JordanAceto/VCF_plug_in_boards/2164_SVF_plug_in_board/pics/pcb_rear.png

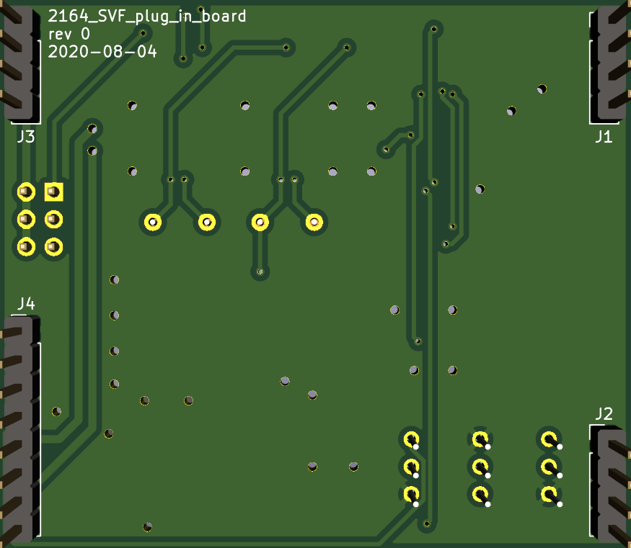
2164_SVF_plug_in_board/pics/pcb_rear.png
