JordanAceto/VCF_plug_in_boards/arp_4072_LPF_plug_in_board/pics/pcb_rear.png

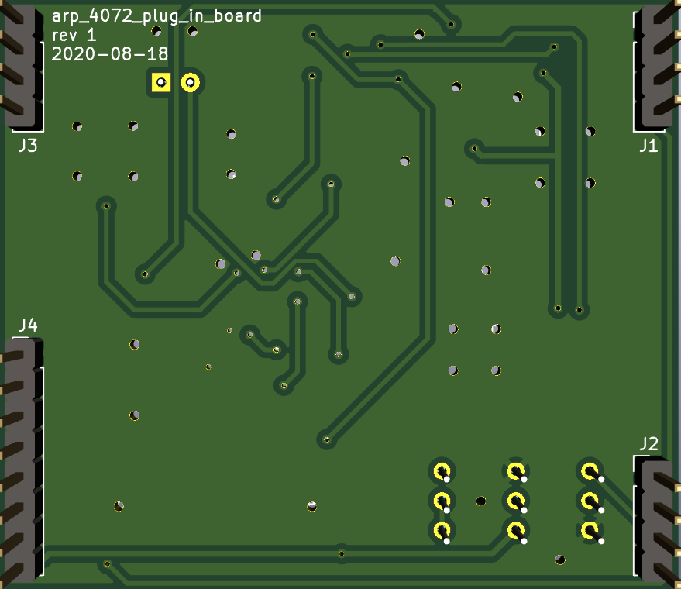
arp_4072_LPF_plug_in_board/pics/pcb_rear.png
