JordanAceto/VCF_plug_in_boards/assets/standard_dimensions.png

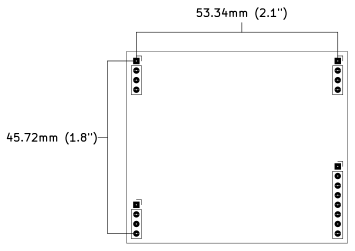
assets/standard_dimensions.png
