JordanAceto/VCF_plug_in_boards/CEM3320_LPF_plug_in_board/pics/pcb_rear.png

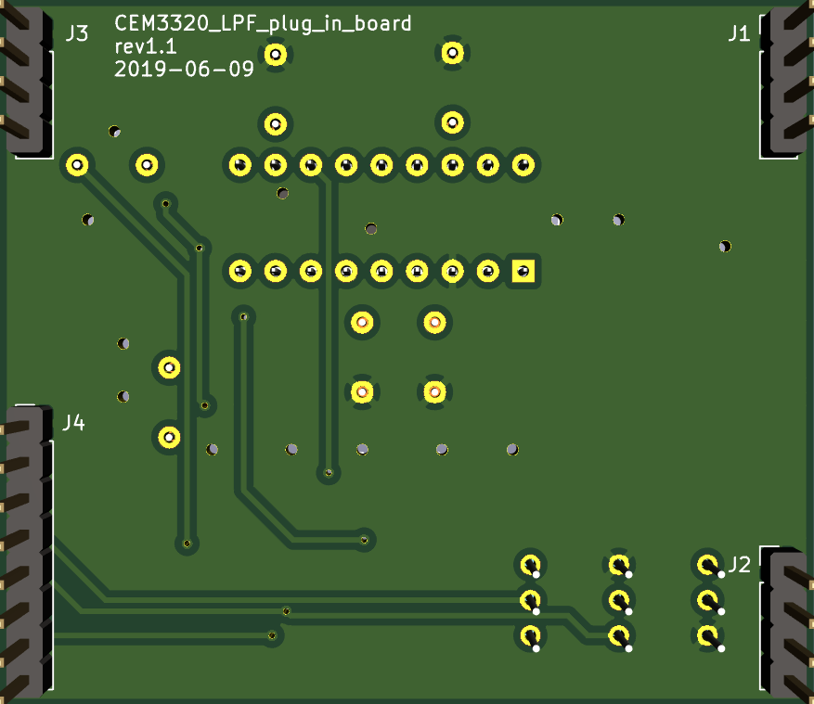
CEM3320_LPF_plug_in_board/pics/pcb_rear.png
