JordanAceto/VCF_plug_in_boards/late_MS20_VCF_plug_in_board/docs/html_nav/images/cat_pcb_bottom_jpg_late_MS20_VCF_plug_in_board-bottom.png

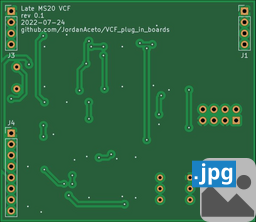
late_MS20_VCF_plug_in_board/docs/html_nav/images/cat_pcb_bottom_jpg_late_MS20_VCF_plug_in_board-bottom.png
