JordanAceto/VCF_plug_in_boards/late_MS20_VCF_plug_in_board/docs/html_nav/images/cat_pcb_top_jpg_late_MS20_VCF_plug_in_board-top.png

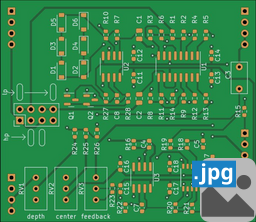
late_MS20_VCF_plug_in_board/docs/html_nav/images/cat_pcb_top_jpg_late_MS20_VCF_plug_in_board-top.png
