JordanAceto/VCF_plug_in_boards/late_MS20_VCF_plug_in_board/docs/html_nav/images/cat_pdf_layers_late_MS20_VCF_plug_in_board-B_Paste.png

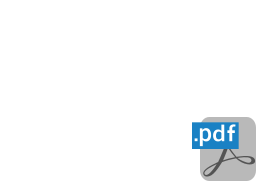
late_MS20_VCF_plug_in_board/docs/html_nav/images/cat_pdf_layers_late_MS20_VCF_plug_in_board-B_Paste.png
