JordanAceto/VCF_plug_in_boards/minimoog_LPF_plug_in_board/docs/html_nav/images/cat_pcb_top_jpg_minimoog_LPF-top.png

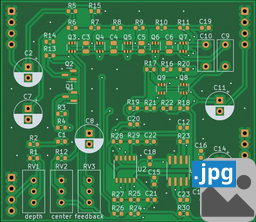
minimoog_LPF_plug_in_board/docs/html_nav/images/cat_pcb_top_jpg_minimoog_LPF-top.png
