JordanAceto/VCF_plug_in_boards/mutron_III_plug_in_board/pics/pcb_rear.png

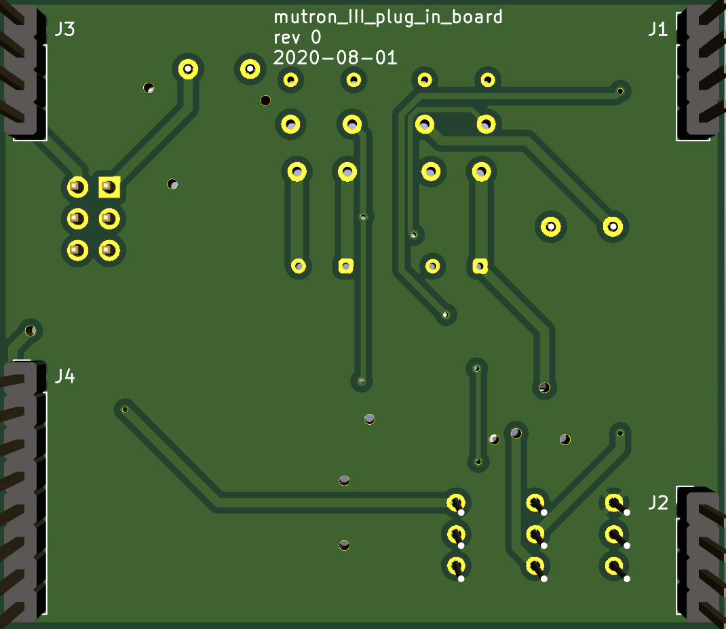
mutron_III_plug_in_board/pics/pcb_rear.png
