JordanAceto/VCF_plug_in_boards/SSI2140_LPF_plug_in_board/pics/pcb_rear.png

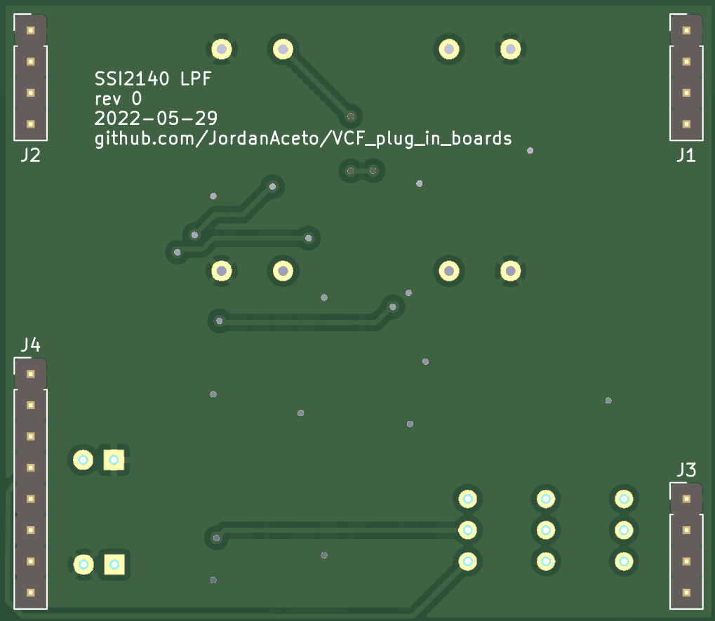
SSI2140_LPF_plug_in_board/pics/pcb_rear.png
