JordanAceto/VCF_plug_in_boards/late_MS20_VCF_plug_in_board/docs/html_nav/images/cat_pdf_sch_print_late_MS20_VCF_plug_in_board-schematic.png

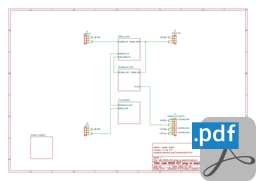
late_MS20_VCF_plug_in_board/docs/html_nav/images/cat_pdf_sch_print_late_MS20_VCF_plug_in_board-schematic.png
