JordanAceto/VCF_plug_in_boards/minimoog_LPF_plug_in_board/docs/html_nav/images/cat_pdf_sch_print_minimoog_LPF-schematic.png

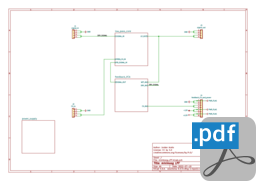
minimoog_LPF_plug_in_board/docs/html_nav/images/cat_pdf_sch_print_minimoog_LPF-schematic.png
