JordanAceto/VCF_plug_in_boards/late_MS20_VCF_plug_in_board/docs/2D/late_MS20_VCF_plug_in_board-F_Cu.pdf

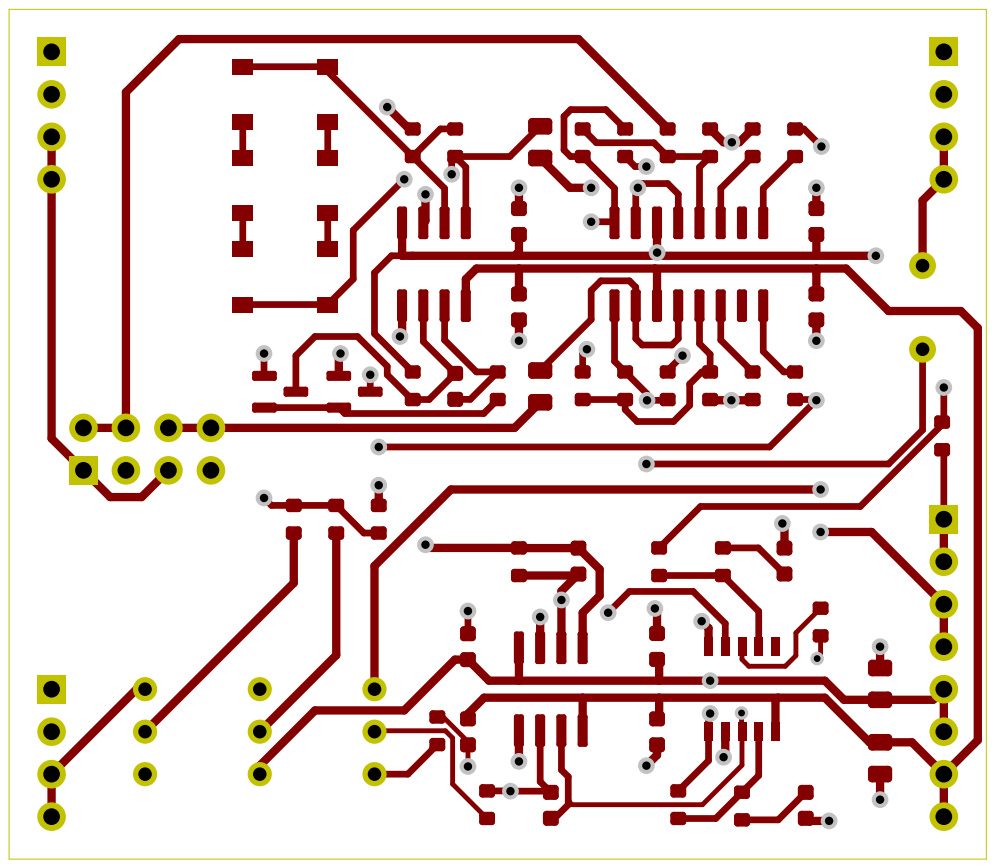
[picture p83: page 1]
