JordanAceto/VCF_plug_in_boards/minimoog_LPF_plug_in_board/docs/2D/minimoog_LPF-B_Cu.pdf

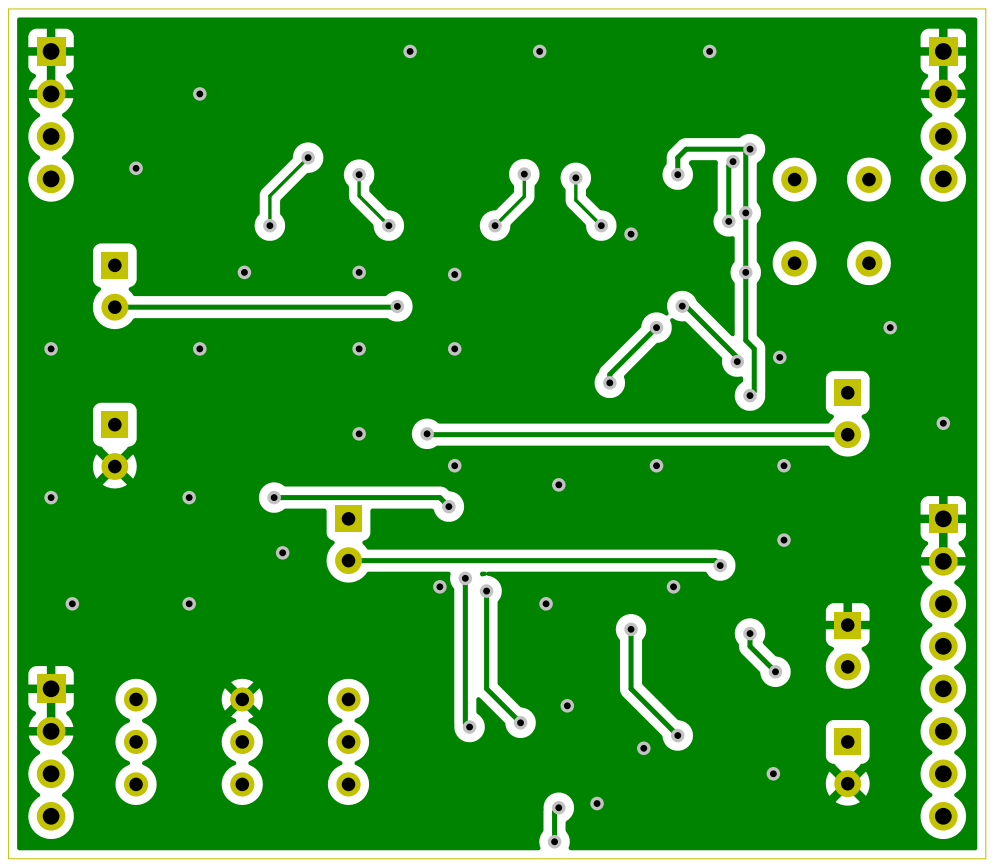
[picture p84: page 1]
