JordanAceto/VCF_plug_in_boards/minimoog_LPF_plug_in_board/docs/2D/minimoog_LPF-F_Cu.pdf

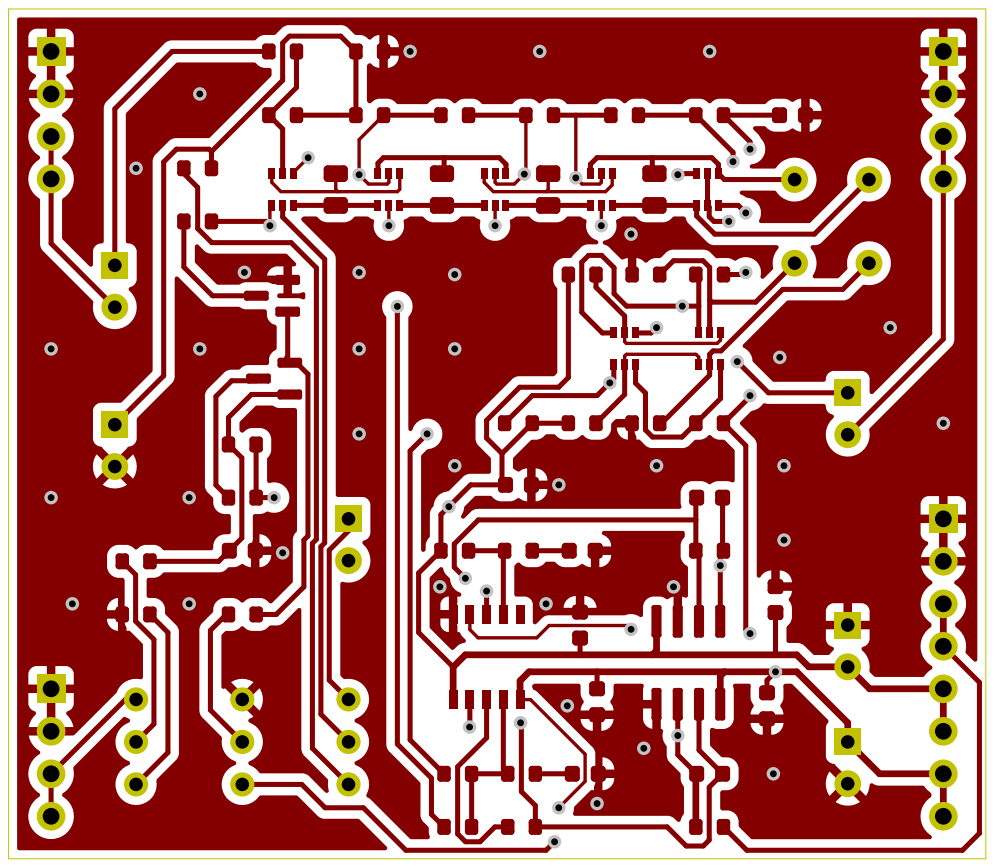
[picture p85: page 1]
