JordanAceto/VCF_plug_in_boards/late_MS20_VCF_plug_in_board/docs/2D/individual_layers/late_MS20_VCF_plug_in_board-B_Fab.pdf

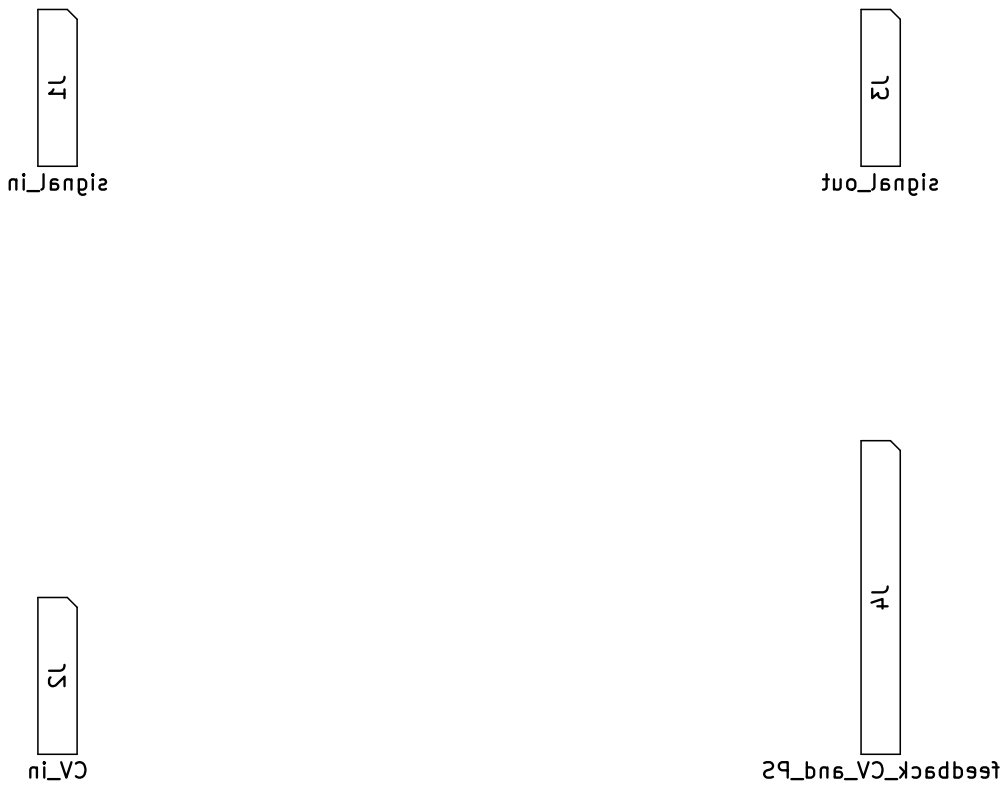
[picture p87: page 1]
