JordanAceto/VCF_plug_in_boards/late_MS20_VCF_plug_in_board/docs/2D/individual_layers/late_MS20_VCF_plug_in_board-B_Silkscreen.pdf

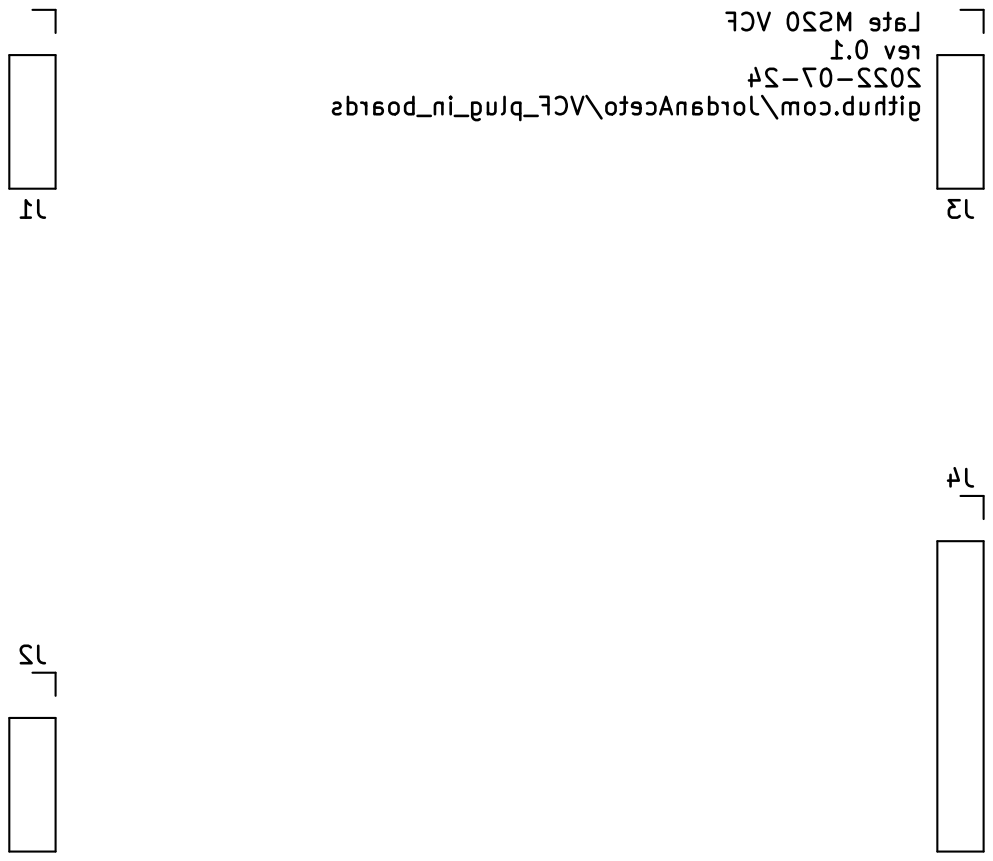
[picture p89: page 1]
