JordanAceto/VCF_plug_in_boards/late_MS20_VCF_plug_in_board/docs/2D/individual_layers/late_MS20_VCF_plug_in_board-F_Courtyard.pdf

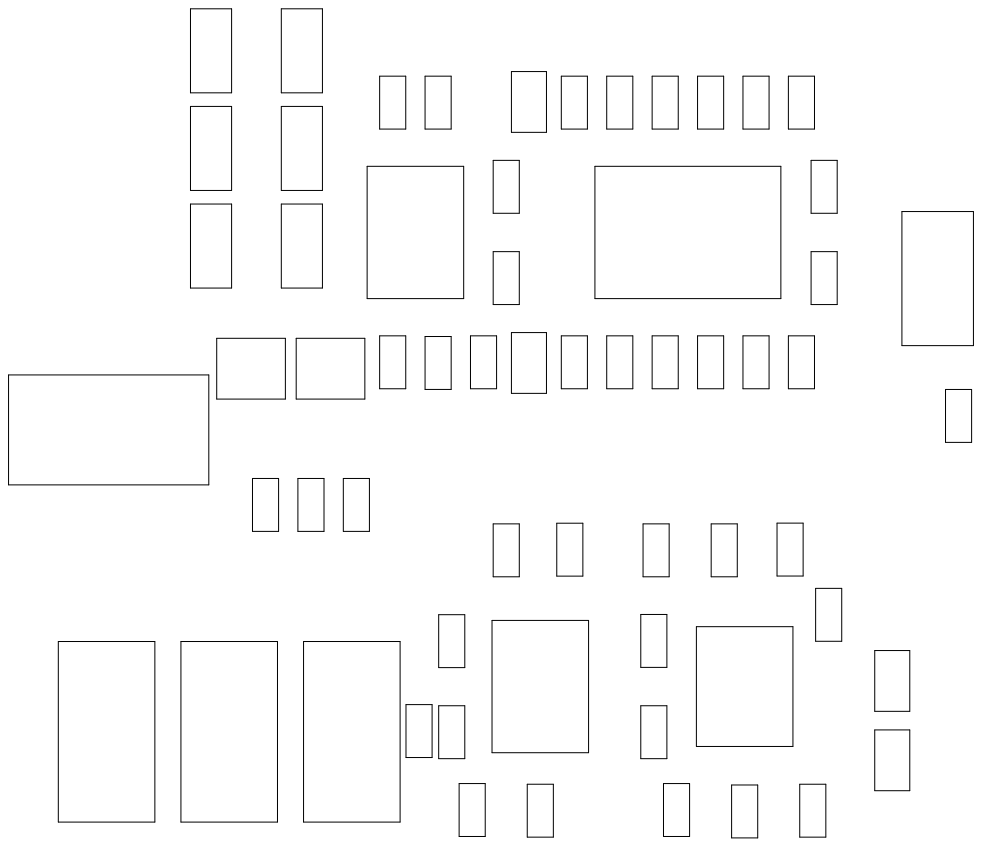
[picture p90: page 1]
