JordanAceto/VCF_plug_in_boards/minimoog_LPF_plug_in_board/docs/2D/individual_layers/minimoog_LPF-B_Mask.pdf

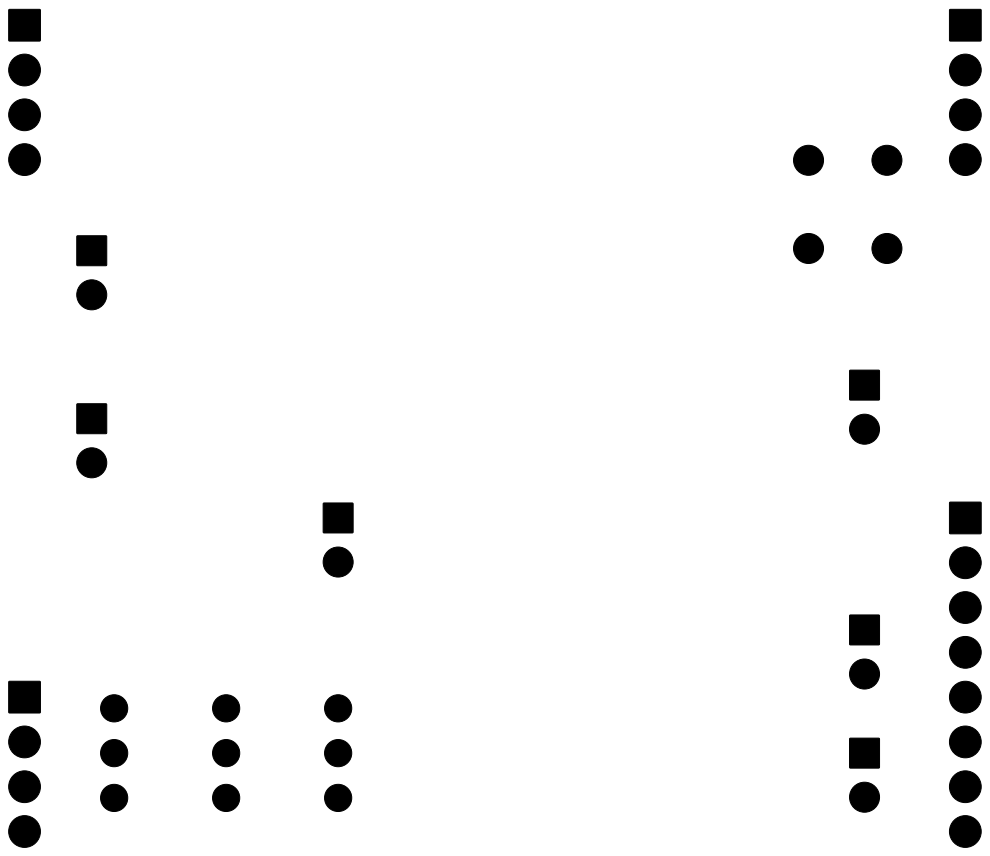
[picture p97: page 1]
