JordanAceto/VCF_plug_in_boards/minimoog_LPF_plug_in_board/docs/2D/individual_layers/minimoog_LPF-F_Courtyard.pdf

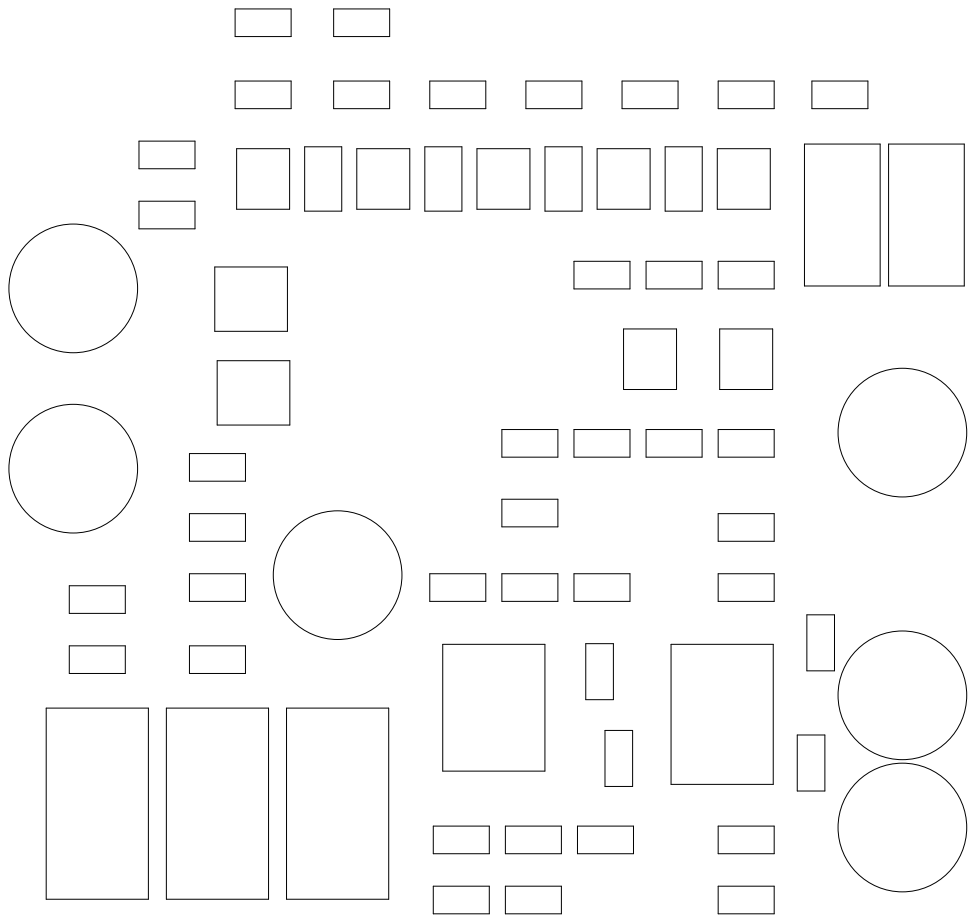
[picture p99: page 1]
