JordanAceto/VCF_plug_in_boards/haible_2040_LPF_plug_in_board/kicad_docs/haible_2040_LPF_plug_in_board.kicad_pcb

## KiCad design haible_2040_LPF_plug_in_board/kicad_docs/haible_2040_LPF_plug_in_board.kicad_pcb (2020-08-01)

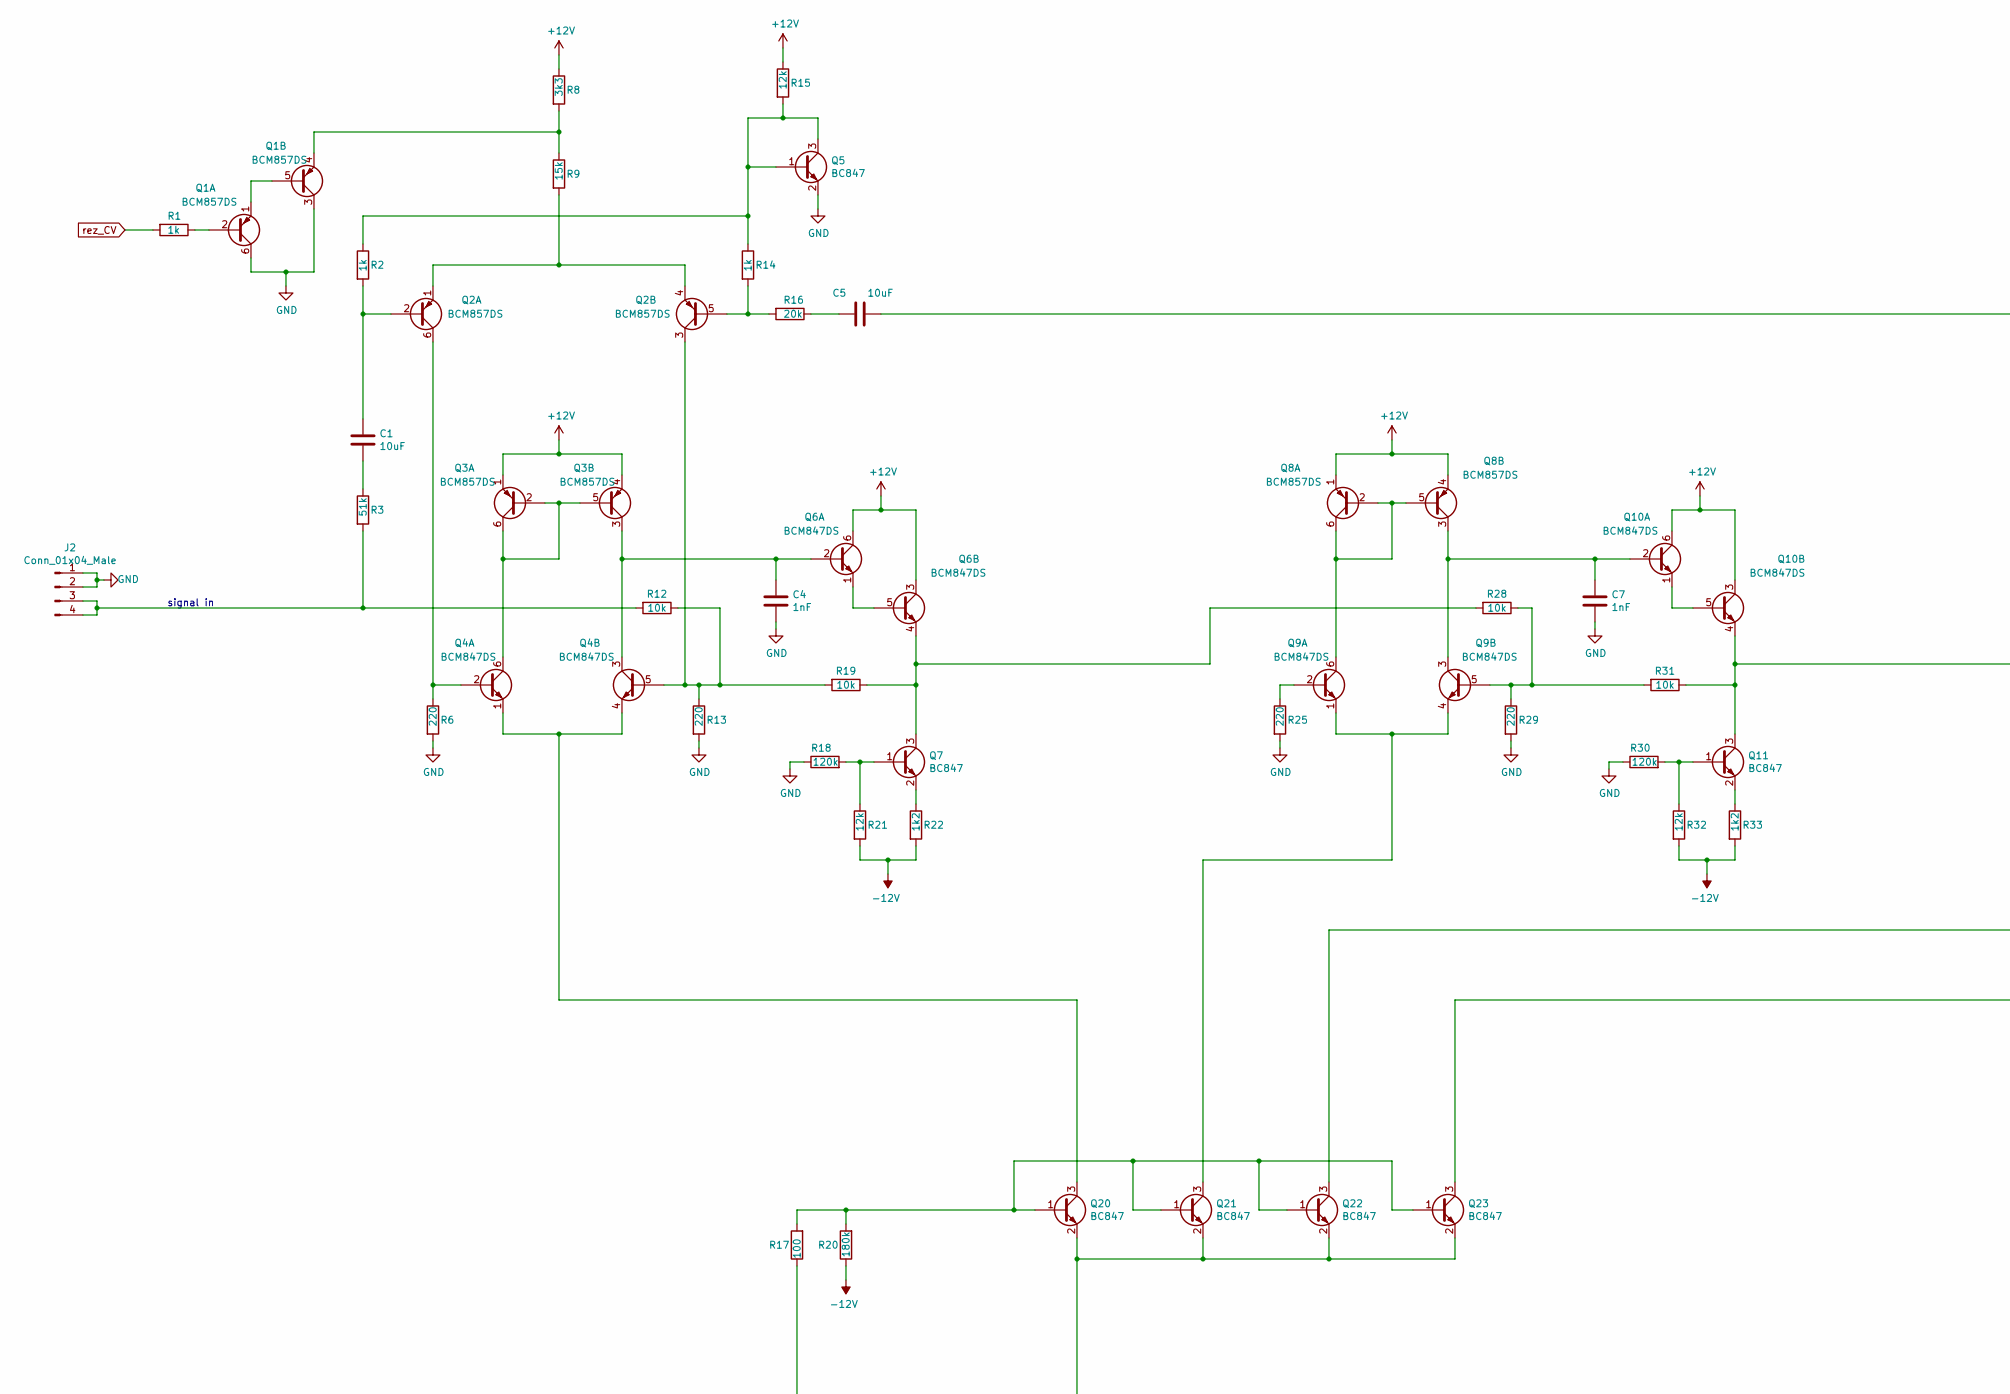
[picture p173: schematic haible_2040_LPF_plug_in_board.sch, Haible 2040 LPF plug-in board, part in row 1, column 1]

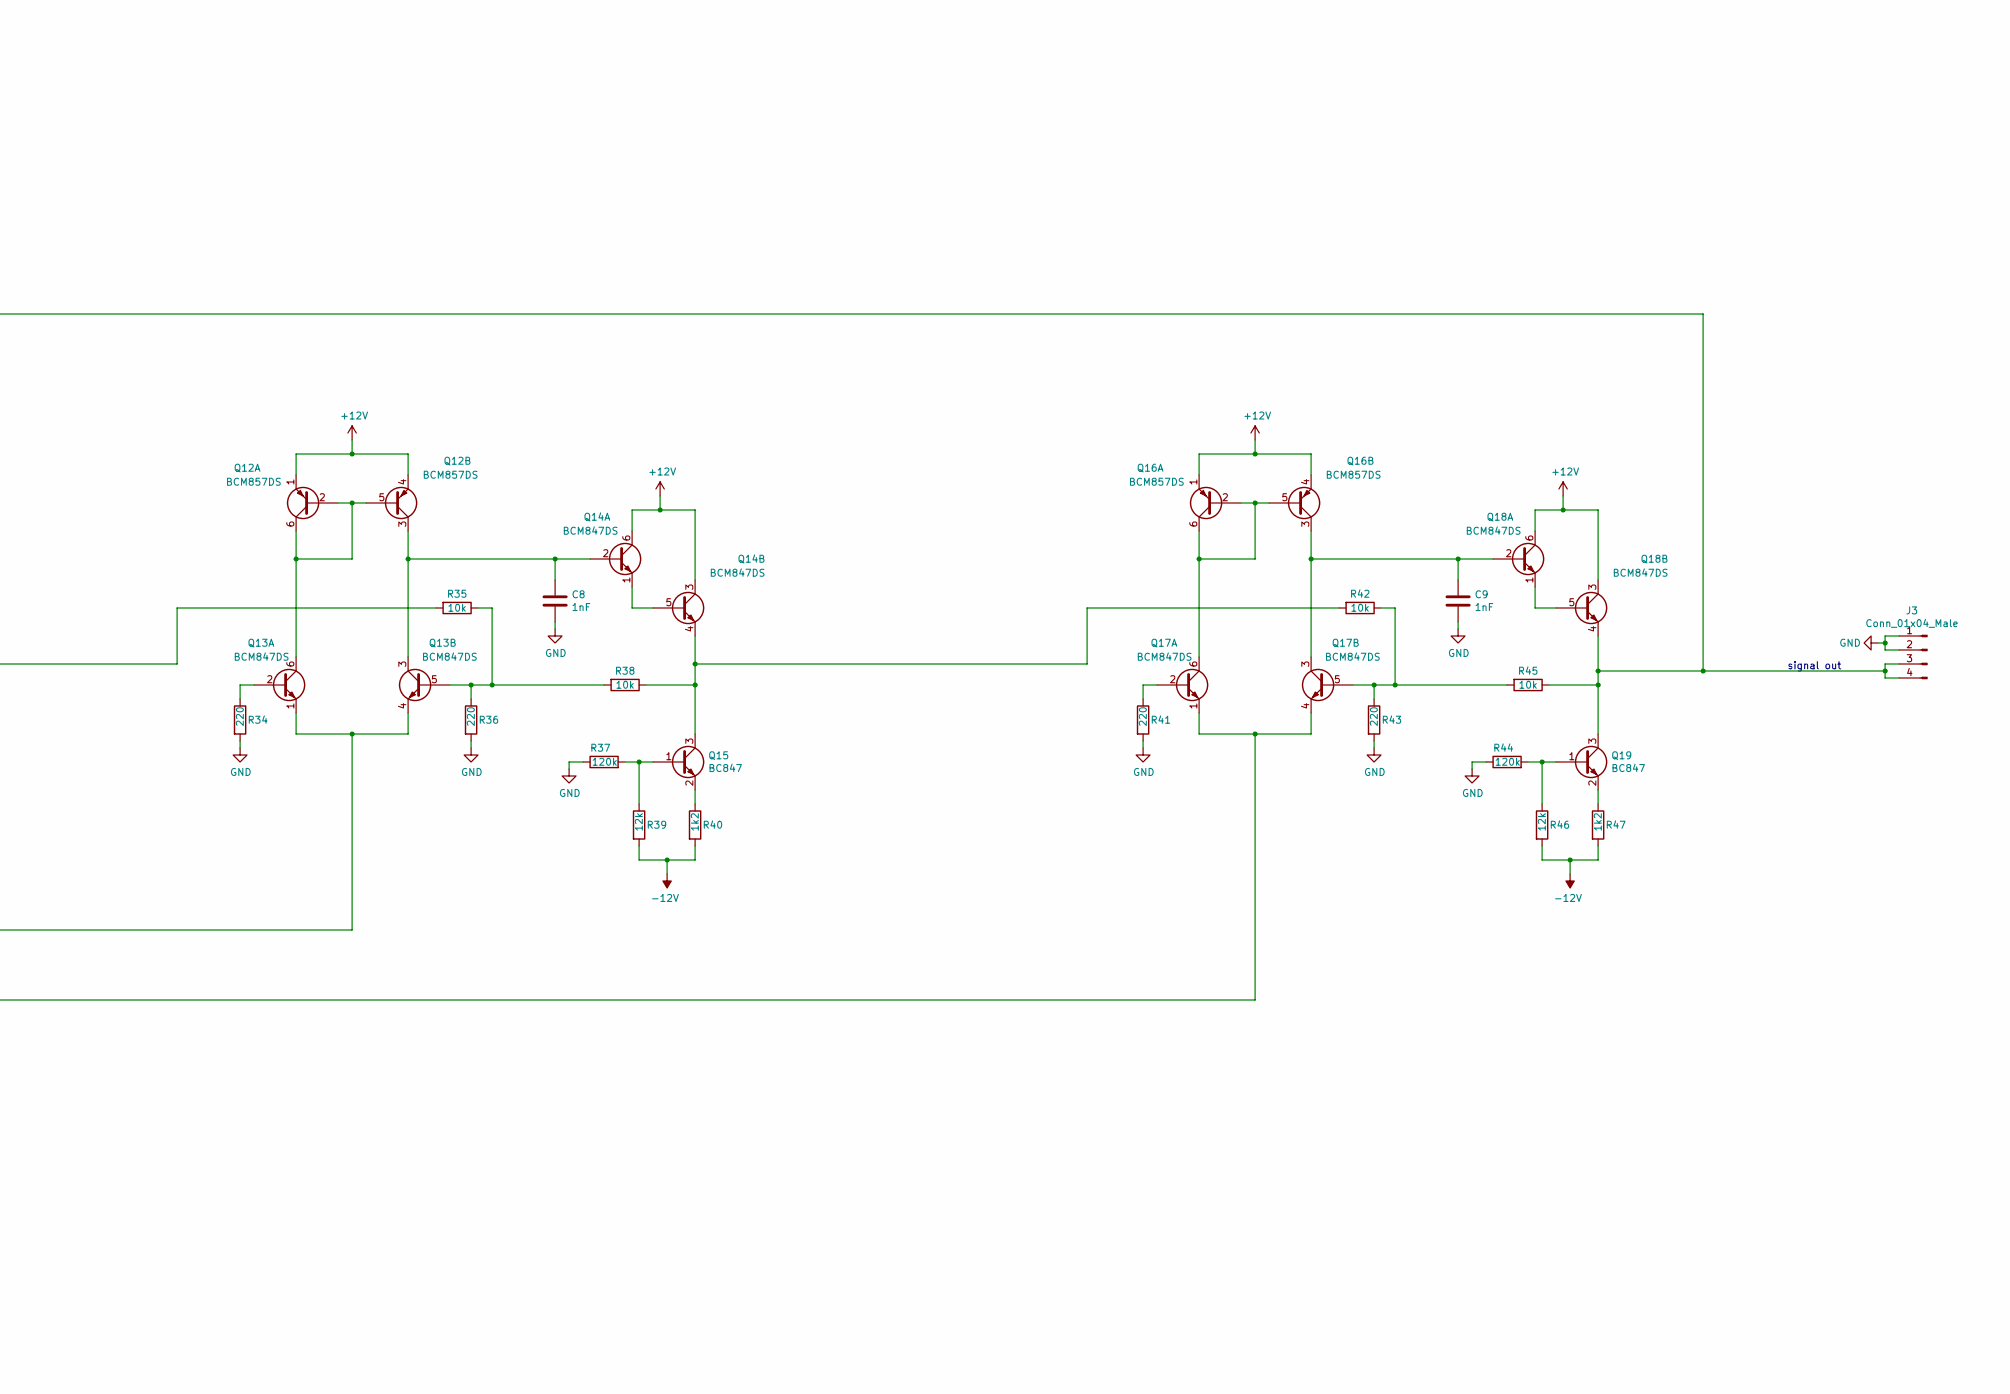
[picture p174: schematic haible_2040_LPF_plug_in_board.sch, Haible 2040 LPF plug-in board, part in row 1, column 2]

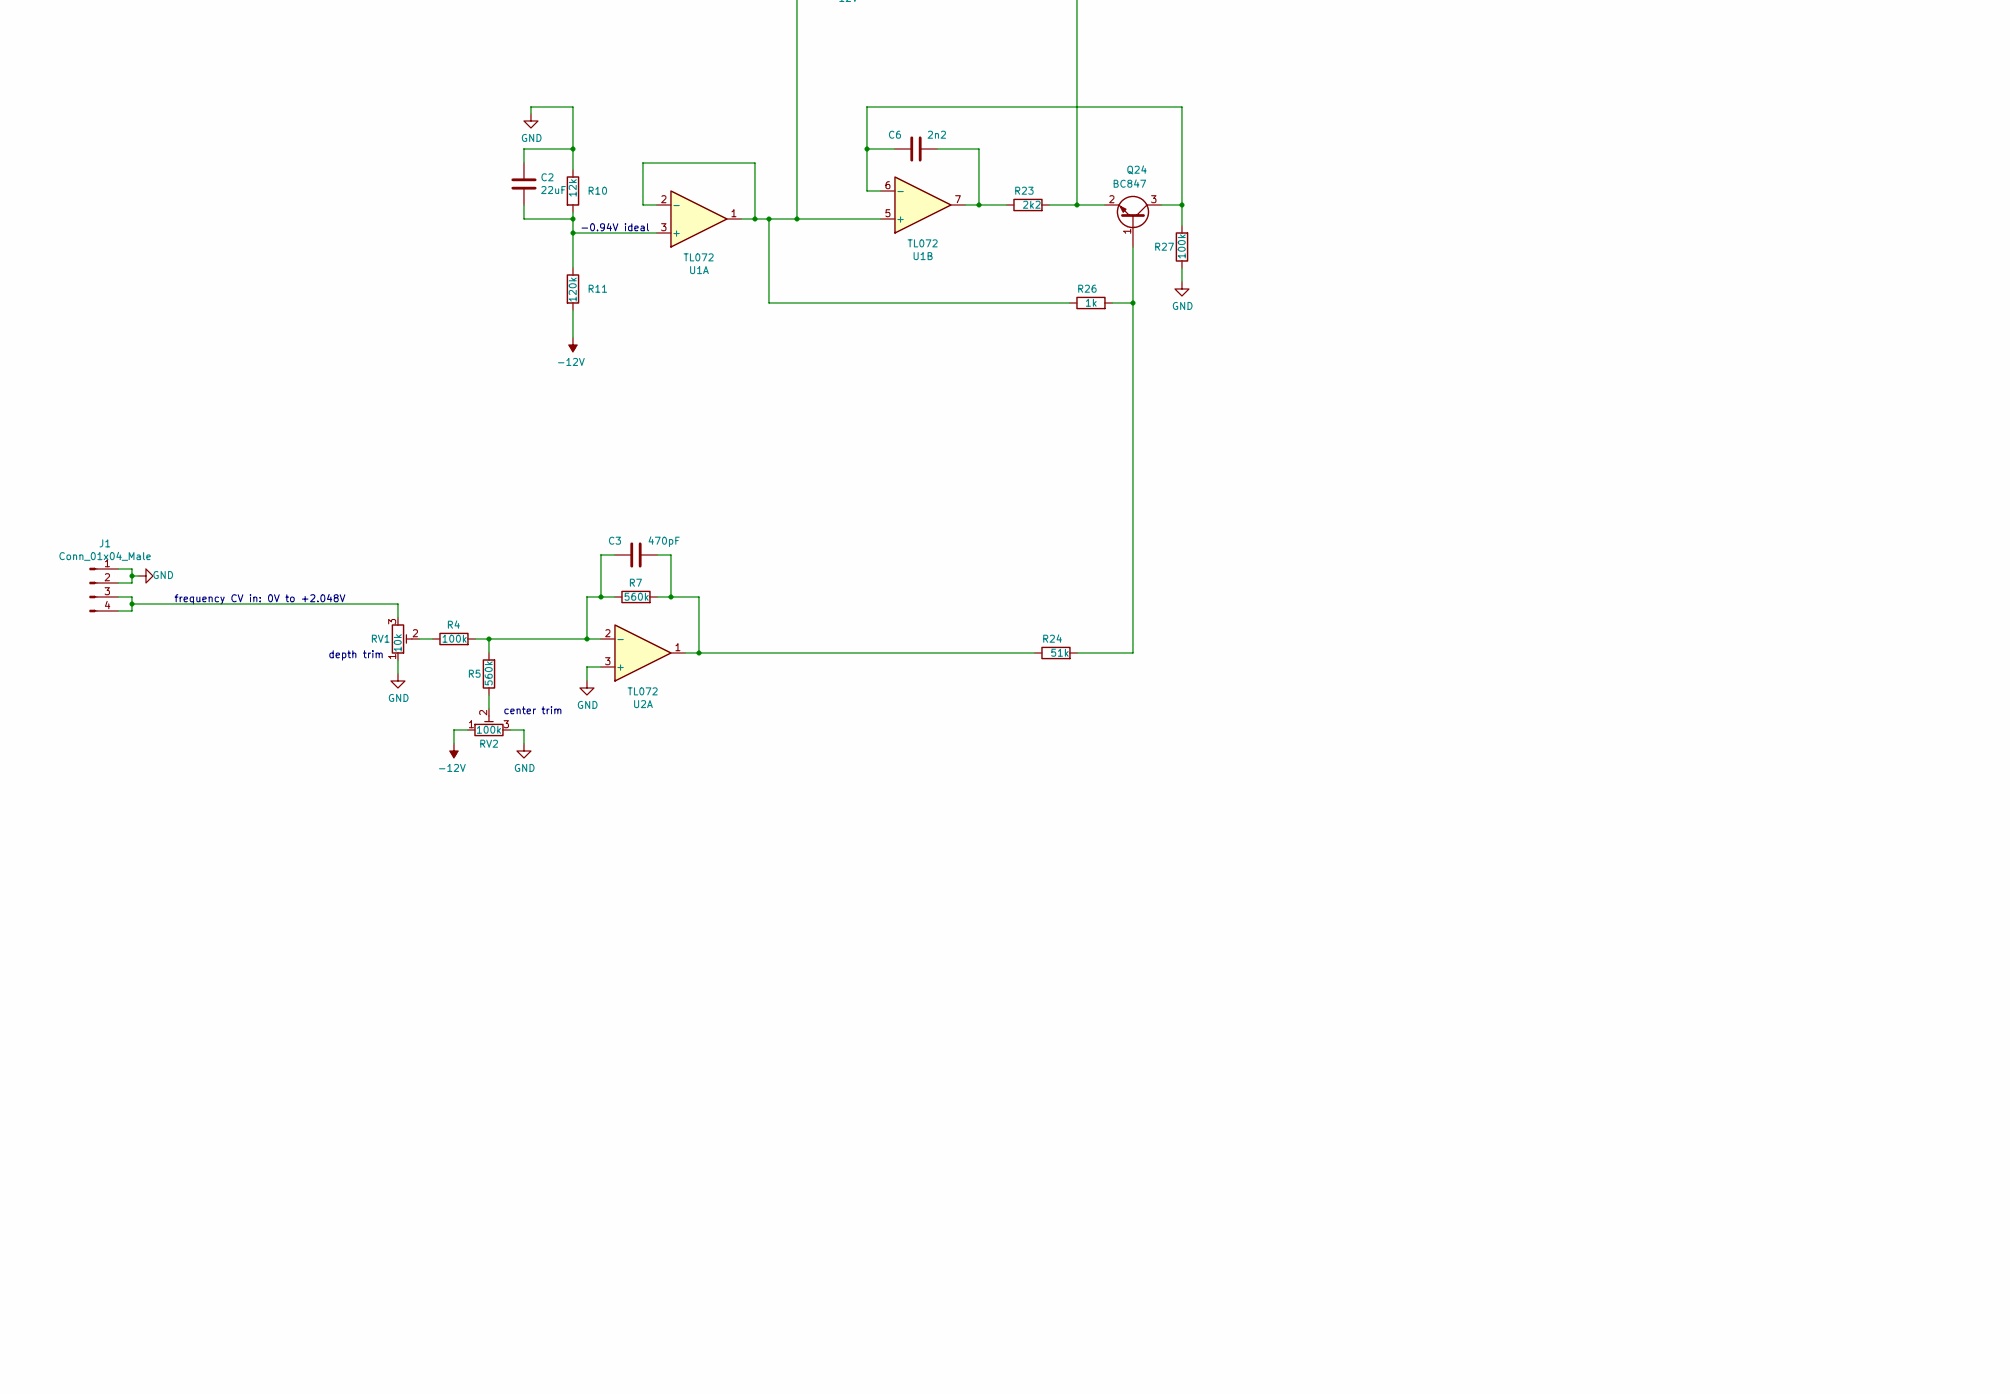
[picture p175: schematic haible_2040_LPF_plug_in_board.sch, Haible 2040 LPF plug-in board, part in row 2, column 1]

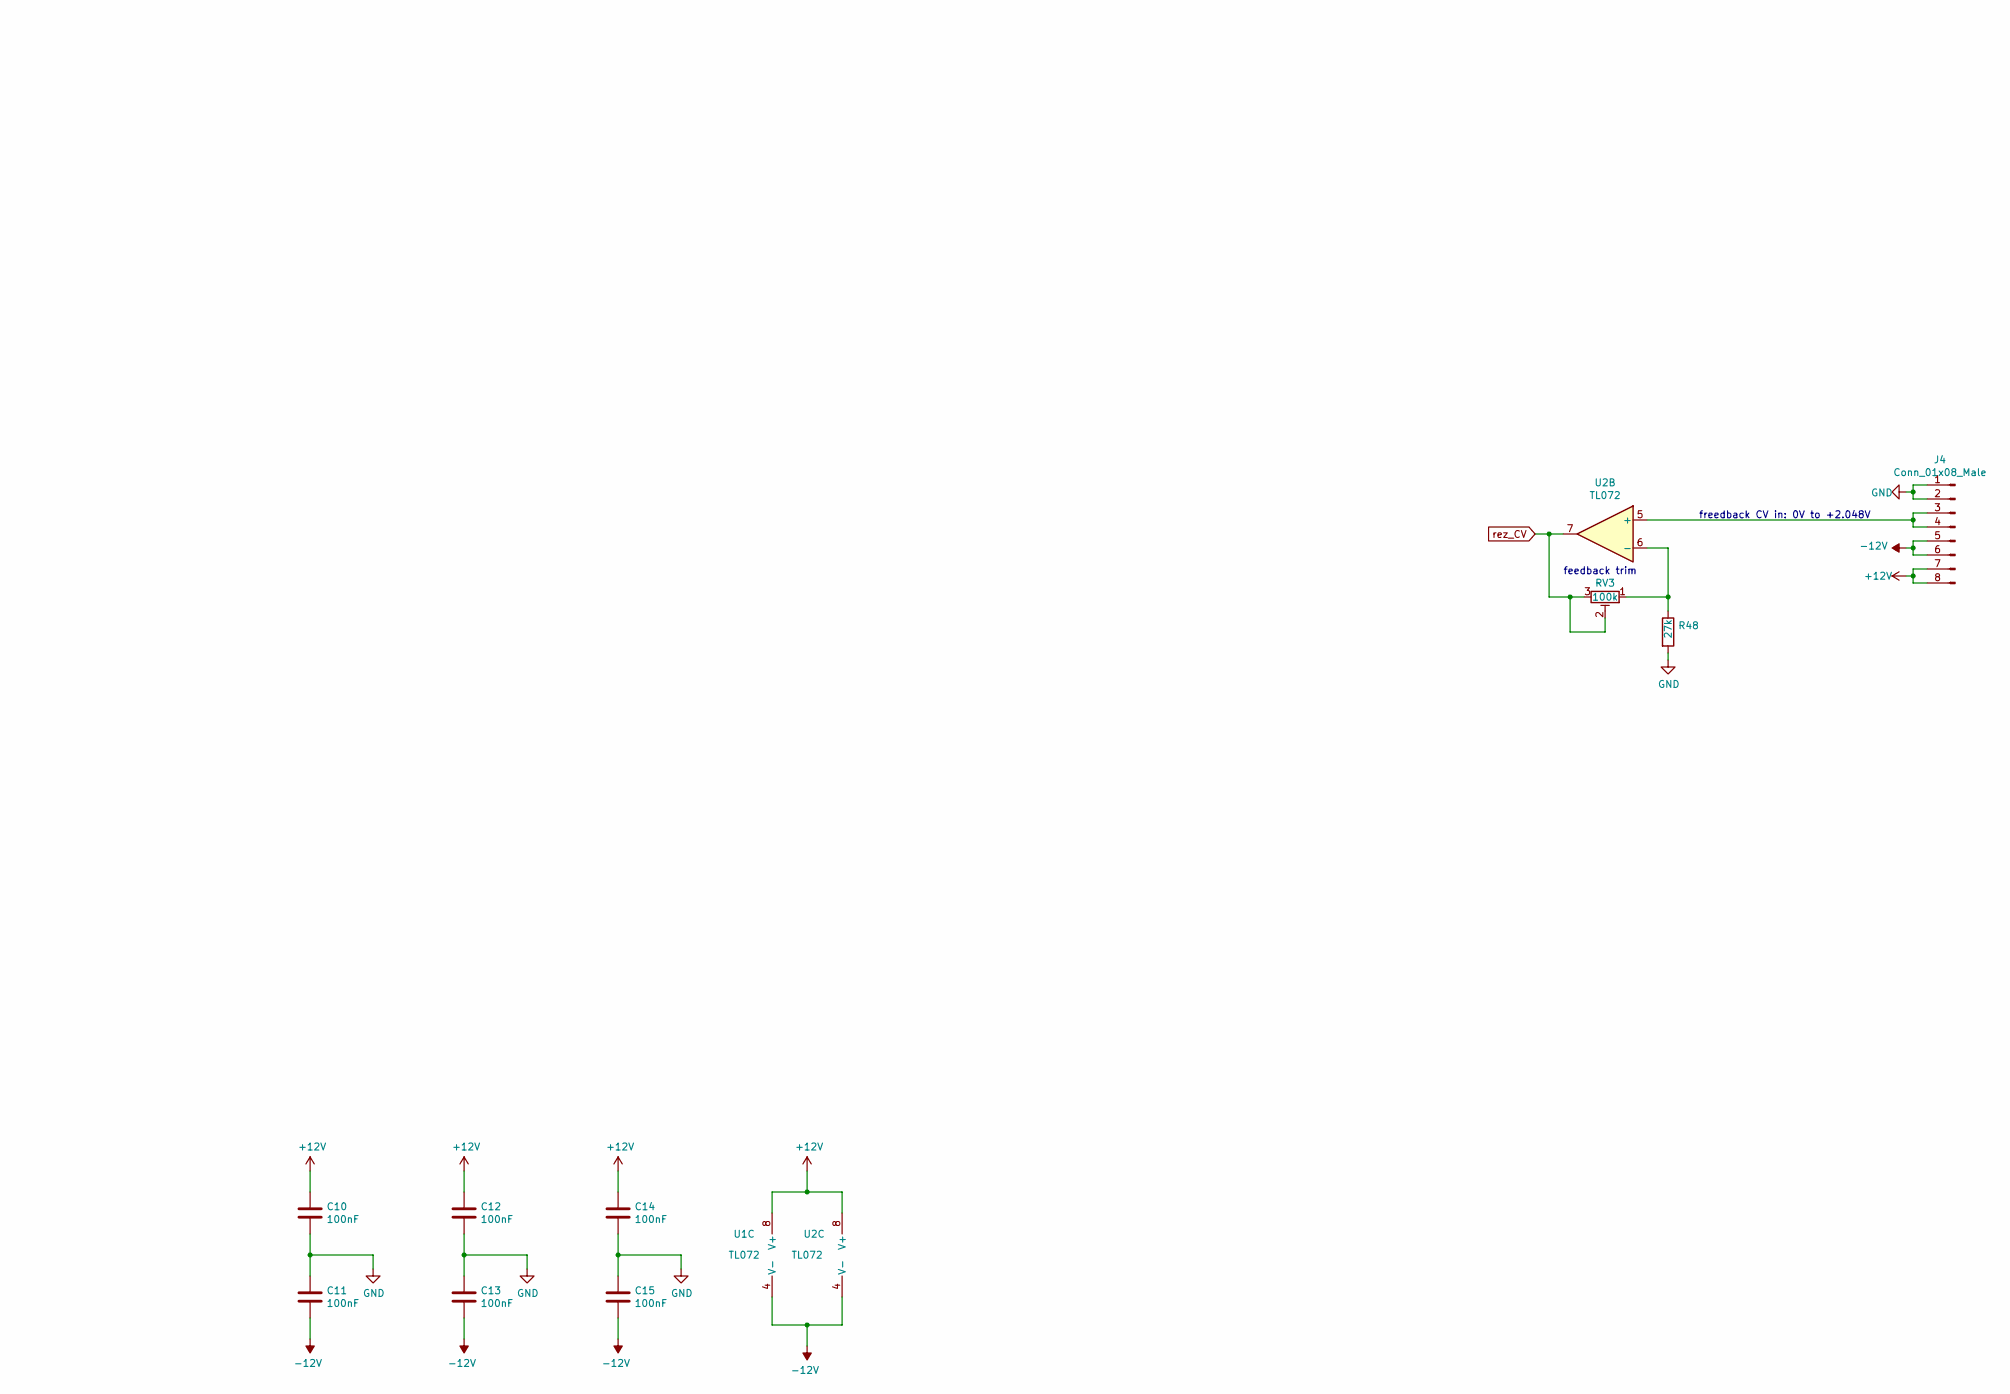
[picture p176: schematic haible_2040_LPF_plug_in_board.sch, Haible 2040 LPF plug-in board, part in row 2, column 2]

Parts:
C1, C5: 10uF; C_Radial_D6.3mm_H11.0mm_P2.50mm
C2: 22uF; C_0805_2012Metric_Pad1.15x1.40mm_HandSolder
C3: 470pF; C_0805_2012Metric_Pad1.15x1.40mm_HandSolder
C4, C7, C8, C9: 1nF; C_0805_2012Metric_Pad1.15x1.40mm_HandSolder
C6: 2n2; C_0805_2012Metric_Pad1.15x1.40mm_HandSolder
C10, C11, C12, C13, C14, C15: 100nF; C_0805_2012Metric_Pad1.15x1.40mm_HandSolder
J1, J2, J3: Conn_01x04_Male; PinHeader_1x04_P2.54mm_Vertical
J4: Conn_01x08_Male; PinHeader_1x08_P2.54mm_Vertical
Q1, Q2, Q3, Q8, Q12, Q16: BCM857DS; SOT457
Q4, Q6, Q9, Q10, Q13, Q14, Q17, Q18: BCM847DS; SOT457
Q5, Q7, Q11, Q15, Q19, Q20, Q21, Q22, Q23, Q24: BC847; SOT-23_Handsoldering
R1, R2, R14, R26: 1k; R_0805_2012Metric_Pad1.15x1.40mm_HandSolder
R3, R24: 51k; R_0805_2012Metric_Pad1.15x1.40mm_HandSolder
R4, R27: 100k; R_0805_2012Metric_Pad1.15x1.40mm_HandSolder
R5, R7: 560k; R_0805_2012Metric_Pad1.15x1.40mm_HandSolder
R6, R13, R25, R29, R34, R36, R41, R43: 220; R_0805_2012Metric_Pad1.15x1.40mm_HandSolder
R8: 3k3; R_0805_2012Metric_Pad1.15x1.40mm_HandSolder
R9: 15k; R_0805_2012Metric_Pad1.15x1.40mm_HandSolder
R10, R15, R21, R32, R39, R46: 12k; R_0805_2012Metric_Pad1.15x1.40mm_HandSolder
R11, R18, R30, R37, R44: 120k; R_0805_2012Metric_Pad1.15x1.40mm_HandSolder
R12, R19, R28, R31, R35, R38, R42, R45: 10k; R_0805_2012Metric_Pad1.15x1.40mm_HandSolder
R16: 20k; R_0805_2012Metric_Pad1.15x1.40mm_HandSolder
R17: 100; R_0805_2012Metric_Pad1.15x1.40mm_HandSolder
R20: 180k; R_0805_2012Metric_Pad1.15x1.40mm_HandSolder
R22, R33, R40, R47: 1k2; R_0805_2012Metric_Pad1.15x1.40mm_HandSolder
R23: 2k2; R_0805_2012Metric_Pad1.15x1.40mm_HandSolder
R48: 27k; R_0805_2012Metric_Pad1.15x1.40mm_HandSolder
RV1: 10k; Potentiometer_Bourns_3269W_Vertical
RV2, RV3: 100k; Potentiometer_Bourns_3269W_Vertical
U1, U2: TL072; SOIC-8_3.9x4.9mm_P1.27mm

Connections:
+12V: C10.1, C12.1, C14.1, J4.7, J4.8, Q3.1 (E), Q3.4 (E), Q6.3 (C), Q6.6 (C), Q8.1 (E), Q8.4 (E), Q10.3 (C), Q10.6 (C), Q12.1 (E), Q12.4 (E), Q14.3 (C), Q14.6 (C), Q16.1 (E), Q16.4 (E), Q18.3 (C), Q18.6 (C), R8.1, R15.1, U1.8 (V+), U2.8 (V+)
-12V: C11.2, C13.2, C15.2, J4.5, J4.6, R11.2, R20.1, R21.2, R22.2, R32.2, R33.2, R39.2, R40.2, R46.2, R47.2, RV2.1, U1.4 (V-), U2.4 (V-)
GND: C2.1, C4.2, C7.2, C8.2, C9.2, C10.2, C11.1, C12.2, C13.1, C14.2, C15.1, J1.1, J1.2, J2.1, J2.2, J3.1, J3.2, J4.1, J4.2, Q1.3 (C), Q1.6 (C), Q5.2 (E), R6.2, R10.1, R13.2, R18.1, R25.2, R27.1, R29.2, R30.1, R34.2, R36.2, R37.1, R41.2, R43.2, R44.1, R48.2, RV1.1, RV2.3, U2.3 (+)
unnamed: C1.1, Q2.2 (B), R2.2
unnamed: C1.2, R3.1
unnamed: C2.2, R10.2, R11.1, U1.3 (+)
unnamed: C3.1, R4.2, R5.2, R7.1, U2.2 (-)
unnamed: C3.2, R7.2, R24.1, U2.1
unnamed: C4.1, Q3.3 (C), Q4.3 (C), Q6.2 (B)
unnamed: C5.1, J3.3, J3.4, Q18.4 (E), Q19.3 (C), R45.1
unnamed: C5.2, R16.1
unnamed: C6.1, Q24.3 (C), R27.2, U1.6 (-)
unnamed: C6.2, R23.1, U1.7
unnamed: C7.1, Q8.3 (C), Q9.3 (C), Q10.2 (B)
unnamed: C8.1, Q12.3 (C), Q13.3 (C), Q14.2 (B)
unnamed: C9.1, Q16.3 (C), Q17.3 (C), Q18.2 (B)
unnamed: J1.3, J1.4, RV1.3
unnamed: J2.3, J2.4, R3.2, R12.2
unnamed: J4.3, J4.4, U2.5 (+)
unnamed: Q1.1 (E), Q1.5 (B)
unnamed: Q1.2 (B), R1.1
unnamed: Q1.4 (E), R8.2, R9.1
unnamed: Q2.1 (E), Q2.4 (E), R9.2
unnamed: Q2.3 (C), Q4.5 (B), R12.1, R13.1, R19.2
unnamed: Q2.5 (B), R14.2, R16.2
unnamed: Q2.6 (C), Q4.2 (B), R6.1
unnamed: Q3.2 (B), Q3.5 (B), Q3.6 (C), Q4.6 (C)
unnamed: Q5.1 (B), Q5.3 (C), R2.1, R14.1, R15.2
unnamed: Q6.1 (E), Q6.5 (B)
unnamed: Q6.4 (E), Q7.3 (C), R19.1, R28.2
unnamed: Q7.1 (B), R18.2, R21.1
unnamed: Q7.2 (E), R22.1
unnamed: Q8.2 (B), Q8.5 (B), Q8.6 (C), Q9.6 (C)
unnamed: Q9.2 (B), R25.1
unnamed: Q9.5 (B), R28.1, R29.1, R31.2
unnamed: Q10.1 (E), Q10.5 (B)
unnamed: Q10.4 (E), Q11.3 (C), R31.1, R35.2
unnamed: Q11.1 (B), R30.2, R32.1
unnamed: Q11.2 (E), R33.1
unnamed: Q12.2 (B), Q12.5 (B), Q12.6 (C), Q13.6 (C)
unnamed: Q13.1 (E), Q13.4 (E), Q22.3 (C)
unnamed: Q13.2 (B), R34.1
unnamed: Q13.5 (B), R35.1, R36.1, R38.2
unnamed: Q14.1 (E), Q14.5 (B)
unnamed: Q14.4 (E), Q15.3 (C), R38.1, R42.2
unnamed: Q15.1 (B), R37.2, R39.1
unnamed: Q15.2 (E), R40.1
unnamed: Q16.2 (B), Q16.5 (B), Q16.6 (C), Q17.6 (C)
unnamed: Q17.1 (E), Q17.4 (E), Q23.3 (C)
unnamed: Q17.2 (B), R41.1
unnamed: Q17.5 (B), R42.1, R43.1, R45.2
unnamed: Q18.1 (E), Q18.5 (B)
unnamed: Q19.1 (B), R44.2, R46.1
unnamed: Q19.2 (E), R47.1
unnamed: Q20.1 (B), Q21.1 (B), Q22.1 (B), Q23.1 (B), R17.2, R20.2
unnamed: Q20.2 (E), Q21.2 (E), Q22.2 (E), Q23.2 (E), Q24.2 (E), R23.2
unnamed: Q4.1 (E), Q4.4 (E), Q20.3 (C)
unnamed: Q9.1 (E), Q9.4 (E), Q21.3 (C)
unnamed: Q24.1 (B), R24.2, R26.2
unnamed: R4.1, RV1.2
unnamed: R5.1, RV2.2
unnamed: R17.1, R26.1, U1.1, U1.2 (-), U1.5 (+)
unnamed: R48.1, RV3.1, U2.6 (-)
rez_CV: R1.2, RV3.2, RV3.3, U2.7

Notes on the sheet:
frequency CV in: 0V to +2.048V
freedback CV in: 0V to +2.048V
depth trim
center trim
-0.94V ideal
feedback trim
signal out
signal in

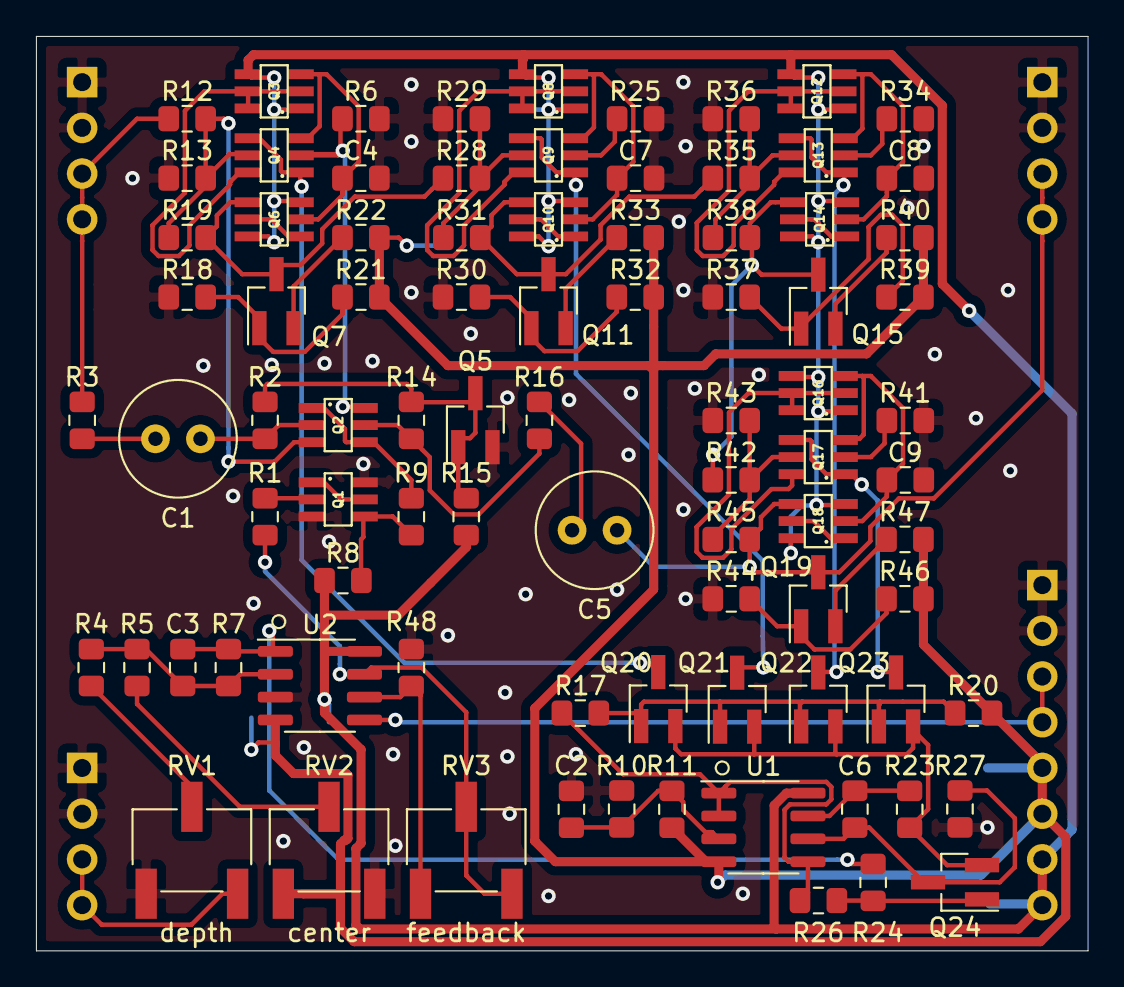
[picture p177: board haible_2040_LPF_plug_in_board.kicad_pcb from above]

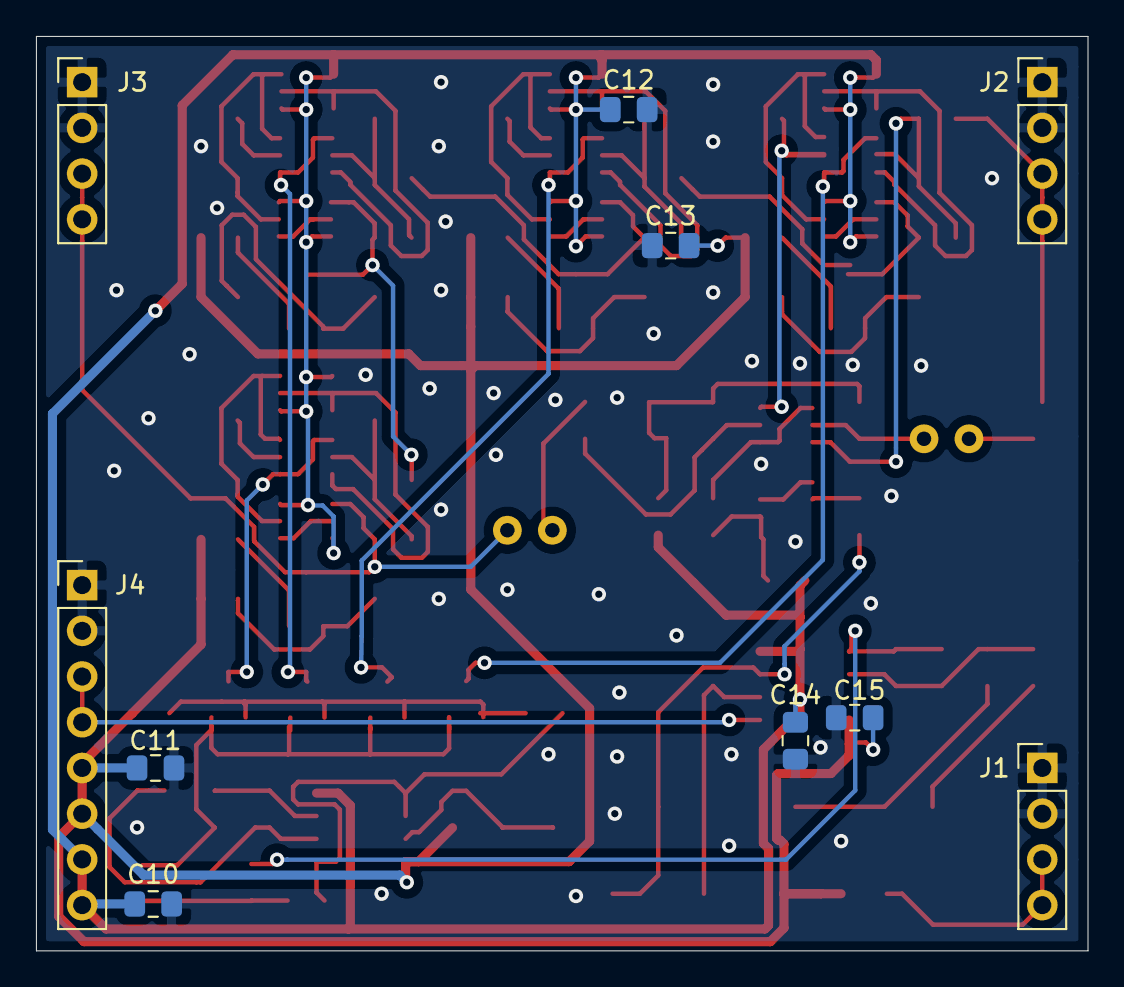
[picture p178: board haible_2040_LPF_plug_in_board.kicad_pcb from below]

Board: 2 copper layers, 58.4 x 50.8 mm, 96 parts (10 on the bottom side), 64 nets.
